michaelobed/rgb-switcher/firmware/main_board/src/mem.c

//
//  mem.c
//  main-board
//
//  Created by michaelobed on 07/02/2025.
//  
//  Copyright © 2025 Michael Obed.

#include "mem.h"

static bool memEmpty = TRUE;
static const uint32_t memSignature = 0x2b005ad1;

static void memEraseAll(void);

static void memEraseAll(void)
{
    for(uint8_t* i = 0x00; i < (uint8_t*)MemAddr_End; i++)
        eeprom_write_byte(i, 0xff);
}

void MemInit(void)
{
    /* Check for the 4-byte signature.
     * If it is correct, we're good. If not, erase everything and reinitialise with the signature. */
    uint32_t memReadValue = 0xffffffff;
    eeprom_read_block(&memReadValue, (const void*)MemAddr_Signature, 4);

    if(memReadValue == memSignature)
        memEmpty = FALSE;
    else
    {
        cli();
        memEraseAll();
        eeprom_update_dword((void*)MemAddr_Signature, memSignature);
        sei();
    }
}

bool MemEmpty(void)
{
    return memEmpty;
}

void MemRead(MemAddr addr, void* data, uint8_t length)
{
    eeprom_read_block(data, (const void*)addr, length);
}

void MemWrite(MemAddr addr, void* data, uint8_t length)
{
    cli();
    eeprom_update_block(data, (void*)addr, length);
    memEmpty = FALSE;
    sei();
}
